JackShkifati28/BloodPressure-Device/images/FullSet1.jpg

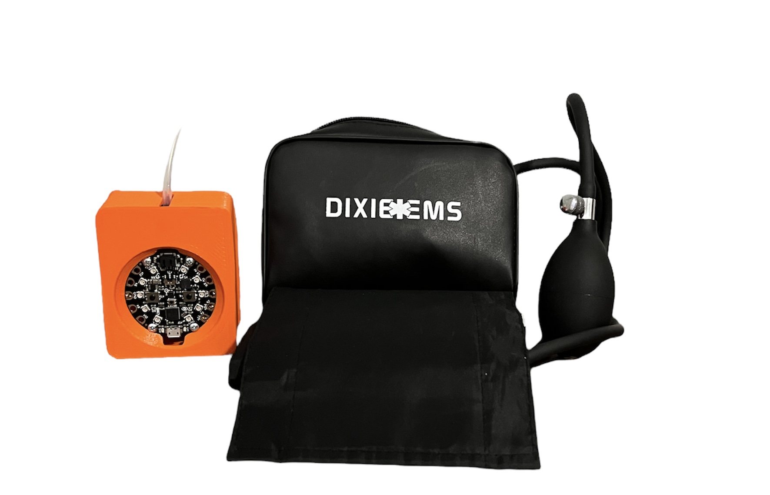
images/FullSet1.jpg
