JackShkifati28/BloodPressure-Device/images/FullSet2.jpg

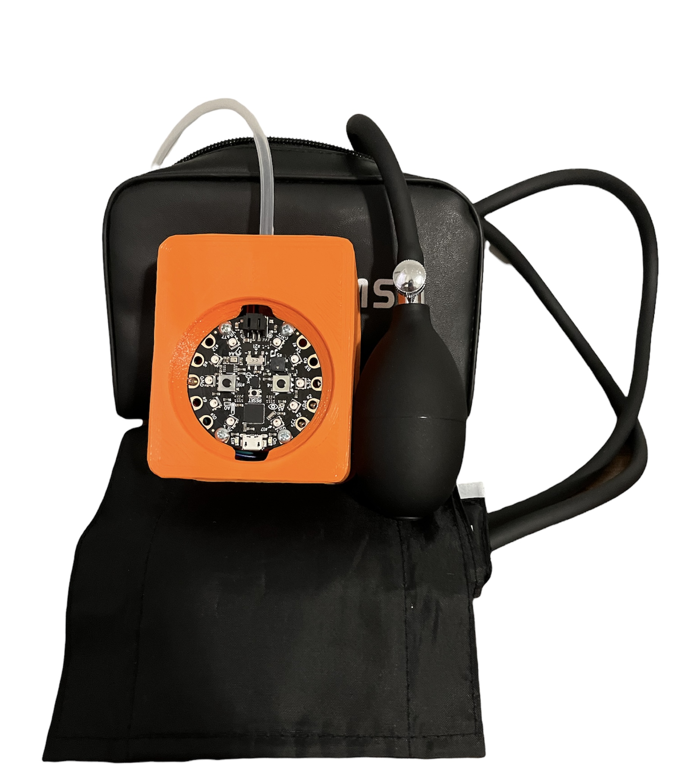
images/FullSet2.jpg
