JackShkifati28/BloodPressure-Device/images/InnerCase.jpg

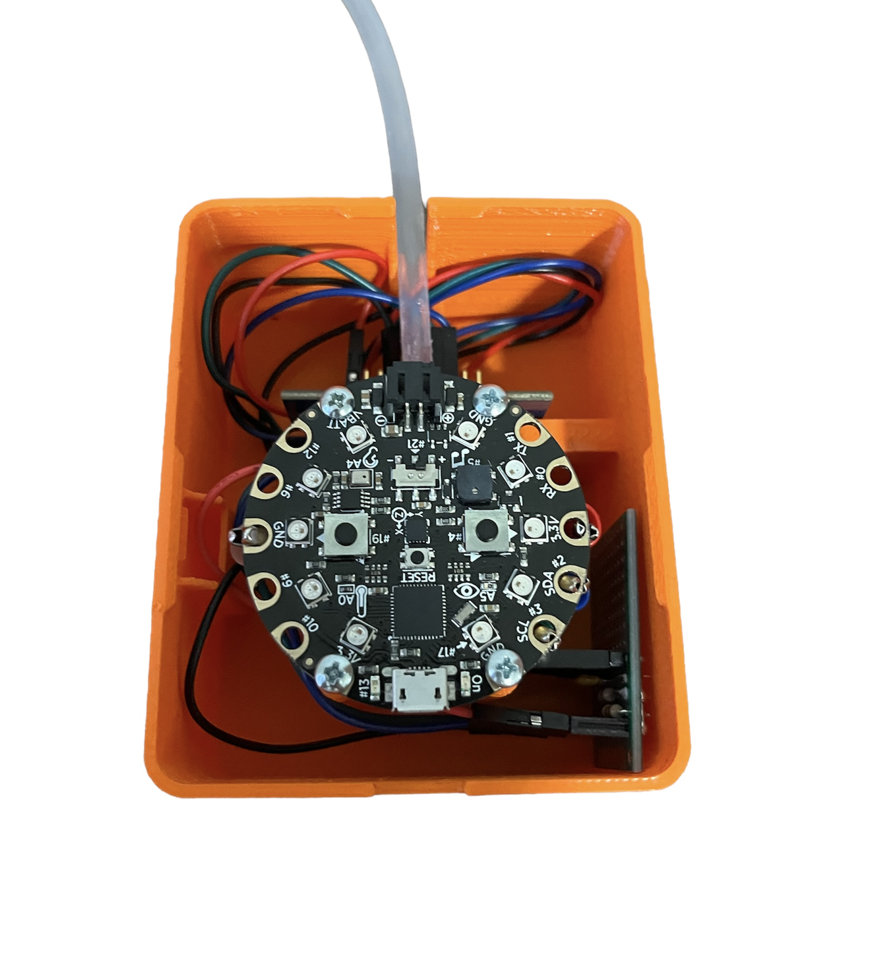
images/InnerCase.jpg
